mean00/WaveFormGenerator_AD9833/include/wavePinout.h

#pragma once

#define AD9833_CS       PB11
#define AD9833_SPI      1    // 2nd one !
#define AD9833_AMP      PA0  // select amplified or not 

#define SSD1306_I2C     0      // 1st one
#define SSD1306_ADR     0x3c   
#define SSD1306_SPEED  (400*1000)   


#define ROTARY_LEFT     PA3 
#define ROTARY_RIGHT    PA2 
#define ROTARY_PUSH     PA1
